antonok-edm/kb/firmware/descriptors.h

/*
             LUFA Library
     Copyright (C) Dean Camera, 2014.

  dean [at] fourwalledcubicle [dot] com
           www.lufa-lib.org
*/

/*
  Copyright 2014  Dean Camera (dean [at] fourwalledcubicle [dot] com)

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
  The author disclaims all warranties with regard to this
  software, including all implied warranties of merchantability
  and fitness.  In no event shall the author be liable for any
  special, indirect or consequential damages or any damages
  whatsoever resulting from loss of use, data or profits, whether
  in an action of contract, negligence or other tortious action,
  arising out of or in connection with the use or performance of
  this software.
*/

#ifndef _DESCRIPTORS_H_
#define _DESCRIPTORS_H_

    /* Includes: */
        #include <avr/pgmspace.h>

        #include <LUFA/Drivers/USB/USB.h>
        #include "custom_hid_class.h"
    /* Type Defines: */
        /** Type define for the device configuration descriptor structure. This must be defined in the
         *  application code, as the configuration descriptor contains several sub-descriptors which
         *  vary between devices, and which describe the device's usage to the host. */
        typedef struct {
            USB_Descriptor_Configuration_Header_t Config;

            // Keyboard HID Interface
            USB_Descriptor_Interface_t            HID_Interface;
            USB_HID_Descriptor_HID_t              HID_KeyboardHID;
            USB_Descriptor_Endpoint_t             HID_ReportINEndpoint;

            // Mouse HID Interface
            USB_Descriptor_Interface_t              HID2_MouseInterface;
            USB_HID_Descriptor_HID_t                HID2_MouseHID;
            USB_Descriptor_Endpoint_t               HID2_ReportINEndpoint;

            // MIDI Audio Control Interface
            USB_Descriptor_Interface_t                Audio_ControlInterface;
            USB_Audio_Descriptor_Interface_AC_t       Audio_ControlInterface_SPC;

            // MIDI Audio Streaming Interface
            USB_Descriptor_Interface_t                Audio_StreamInterface;
            USB_MIDI_Descriptor_AudioInterface_AS_t   Audio_StreamInterface_SPC;
            USB_MIDI_Descriptor_InputJack_t           MIDI_In_Jack_Emb;
            USB_MIDI_Descriptor_InputJack_t           MIDI_In_Jack_Ext;
            USB_MIDI_Descriptor_OutputJack_t          MIDI_Out_Jack_Emb;
            USB_MIDI_Descriptor_OutputJack_t          MIDI_Out_Jack_Ext;
            USB_Audio_Descriptor_StreamEndpoint_Std_t MIDI_In_Jack_Endpoint;
            USB_MIDI_Descriptor_Jack_Endpoint_t       MIDI_In_Jack_Endpoint_SPC;
            USB_Audio_Descriptor_StreamEndpoint_Std_t MIDI_Out_Jack_Endpoint;
            USB_MIDI_Descriptor_Jack_Endpoint_t       MIDI_Out_Jack_Endpoint_SPC;
        } USB_Descriptor_Configuration_t;

        /** Enum for the device interface descriptor IDs within the device. Each interface descriptor
         *  should have a unique ID index associated with it, which can be used to refer to the
         *  interface from other descriptors. */
        enum InterfaceDescriptors_t
        {
            INTERFACE_ID_Keyboard = 0,     /**< Keyboard interface descriptor ID */
            INTERFACE_ID_Mouse = 1,        /**< Mouse interface descriptor ID */
            INTERFACE_ID_AudioControl = 3, /**< Audio control interface descriptor ID */
            INTERFACE_ID_AudioStream  = 4, /**< Audio streaming interface descriptor ID */
        };

        /** Enum for the device string descriptor IDs within the device. Each string descriptor should
         *  have a unique ID index associated with it, which can be used to refer to the string from
         *  other descriptors. */
        enum StringDescriptors_t
        {
            STRING_ID_Language     = 0, /**< Supported Languages string descriptor ID (must be zero) */
            STRING_ID_Manufacturer = 1, /**< Manufacturer string ID */
            STRING_ID_Product      = 2, /**< Product string ID */
        };

    /* Macros for HID: */
        /** Endpoint address of the Keyboard HID reporting IN endpoint. */
        #define KEYBOARD_EPADDR              (ENDPOINT_DIR_IN | 1)

        /** Size in bytes of the Keyboard HID reporting IN endpoint. */
        #define KEYBOARD_EPSIZE              64

        /** Endpoint address of the Mouse HID reporting IN endpoint. */
        #define MOUSE_IN_EPADDR              (ENDPOINT_DIR_IN | 4)

        /** Size in bytes of the Mouse HID reporting IN endpoint */
        #define MOUSE_EPSIZE                 64

    /* Macros for MIDI: */
        /** Endpoint address of the MIDI streaming data IN endpoint, for device-to-host data transfers. */
        #define MIDI_STREAM_IN_EPADDR       (ENDPOINT_DIR_IN  | 3)

        /** Endpoint address of the MIDI streaming data OUT endpoint, for host-to-device data transfers. */
        #define MIDI_STREAM_OUT_EPADDR      (ENDPOINT_DIR_OUT | 2)

        /** Endpoint size in bytes of the Audio isochronous streaming data IN and OUT endpoints. */
        #define MIDI_STREAM_EPSIZE          64

    /* Function Prototypes: */
        uint16_t CALLBACK_USB_GetDescriptor(const uint16_t wValue,
                                            const uint16_t wIndex,
                                            const void** const DescriptorAddress)
                                            ATTR_WARN_UNUSED_RESULT ATTR_NON_NULL_PTR_ARG(3);

#endif
